CDFER/JLCPCB-Kicad-Library/JLCPCB-Kicad-Footprints/3dModels/CAP-TH_BD8.0-P3.50-D0.6-FD_1.step

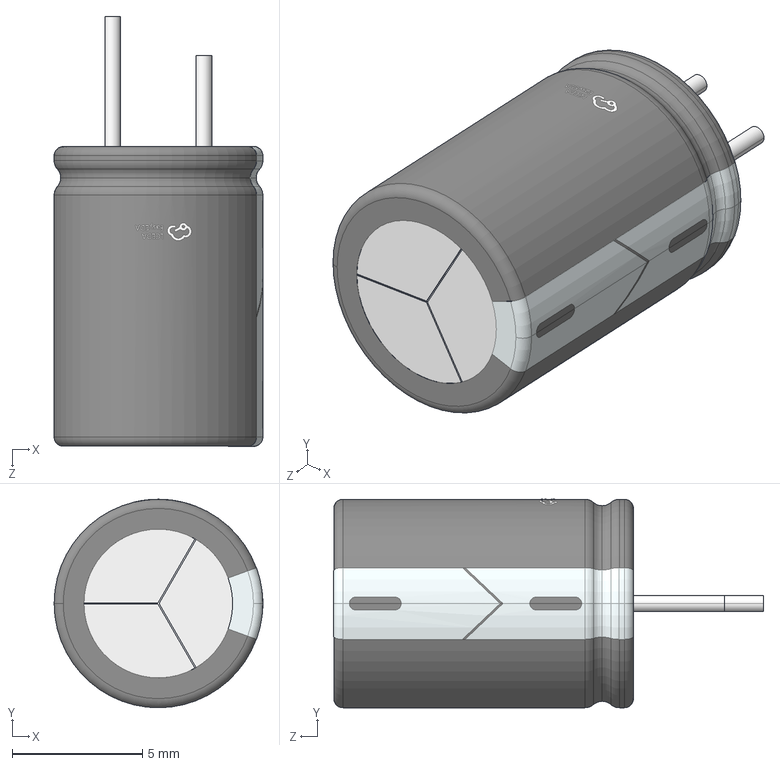
[picture p15: CAD file, 2024-11-15]
JLCPCB-Kicad-Footprints/3dModels/CAP-TH_BD8.0-P3.50-D0.6-FD_1.step
8.01 x 8.00 x 16.5 mm
