CDFER/JLCPCB-Kicad-Library/JLCPCB-Kicad-Footprints/3dModels/RES-SMD_L10.0-W5.2.step

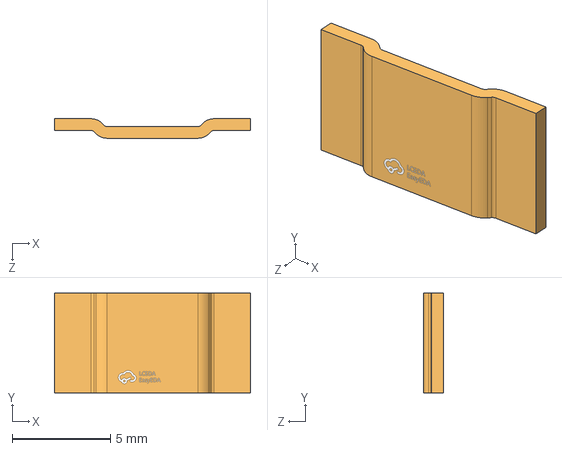
[picture p16: CAD file, 2024-11-15]
JLCPCB-Kicad-Footprints/3dModels/RES-SMD_L10.0-W5.2.step
10.0 x 5.10 x 1.00 mm
