CDFER/JLCPCB-Kicad-Library/JLCPCB-Kicad-Footprints/3dModels/SDB_L8.3-W6.4-P5.10-LS9.9-BL.step

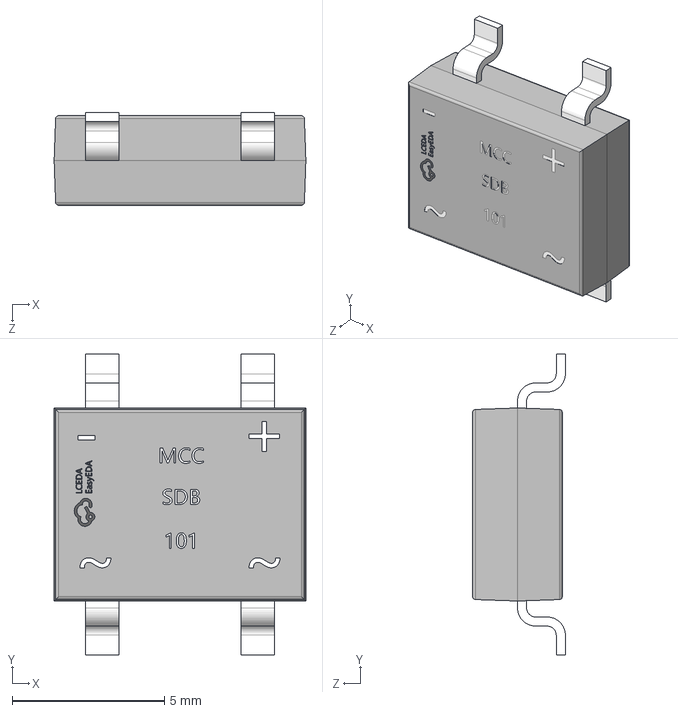
[picture p17: CAD file, 2024-11-15]
JLCPCB-Kicad-Footprints/3dModels/SDB_L8.3-W6.4-P5.10-LS9.9-BL.step
8.28 x 9.90 x 3.05 mm
