CDFER/JLCPCB-Kicad-Library/JLCPCB-Kicad-Footprints/3dModels/IND-SMD_L13.8-W12.6_YSPI13XX.step

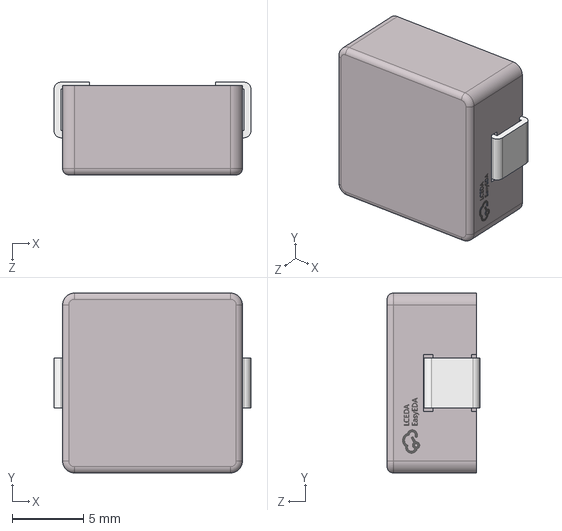
[picture p18: CAD file, 2024-11-15]
JLCPCB-Kicad-Footprints/3dModels/IND-SMD_L13.8-W12.6_YSPI13XX.step
13.8 x 12.6 x 6.50 mm
