CDFER/JLCPCB-Kicad-Library/JLCPCB-Kicad-Footprints/3dModels/CAP-TH_L5.0-W3.2-P5.08-D0.6.step

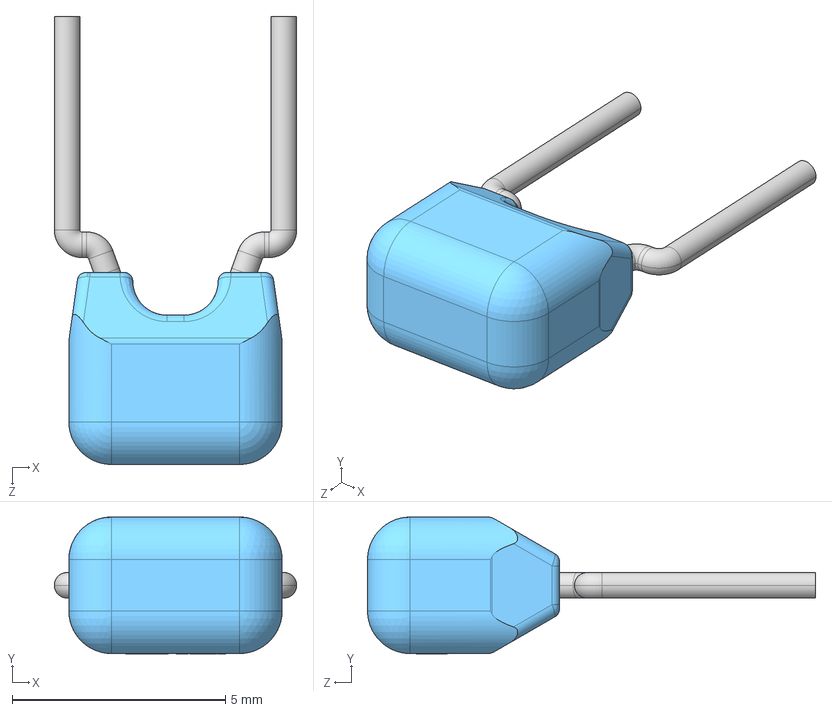
[picture p19: CAD file, 2024-11-15]
JLCPCB-Kicad-Footprints/3dModels/CAP-TH_L5.0-W3.2-P5.08-D0.6.step
5.68 x 3.21 x 10.5 mm
