CDFER/JLCPCB-Kicad-Library/JLCPCB-Kicad-Footprints/3dModels/CAP-TH_BD10.0-P5.00-D0.6-FD.step

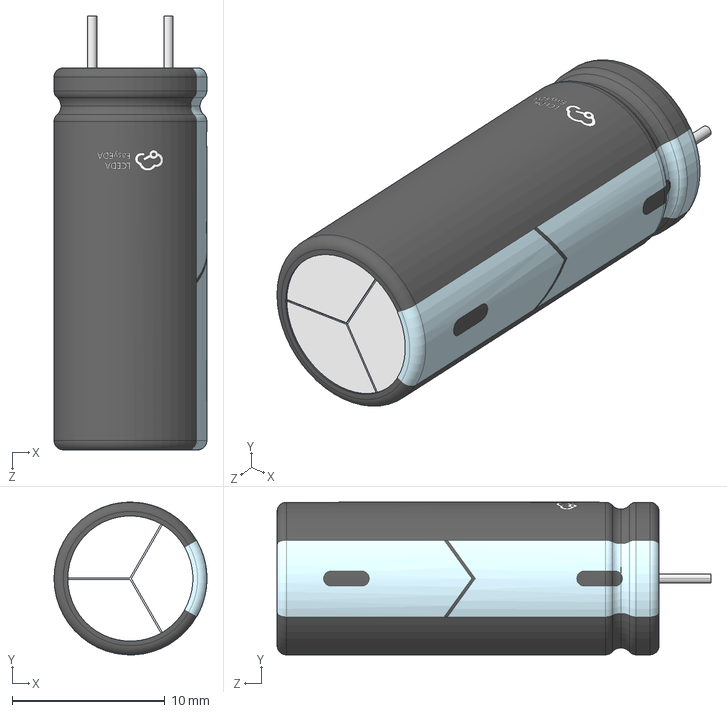
[picture p20: CAD file, 2024-11-15]
JLCPCB-Kicad-Footprints/3dModels/CAP-TH_BD10.0-P5.00-D0.6-FD.step
10.0 x 9.99 x 28.4 mm
