CDFER/JLCPCB-Kicad-Library/JLCPCB-Kicad-Footprints/3dModels/SOT-669_L4.9-W4.0-P1.27-LS6.0-BR.step

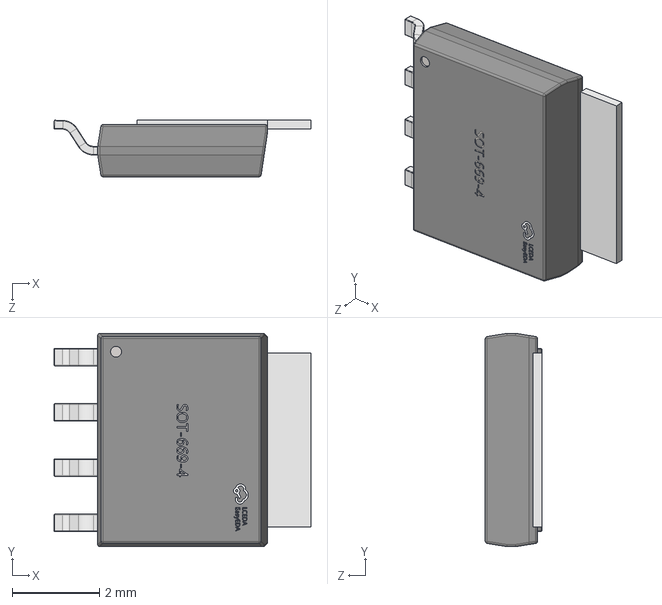
[picture p21: CAD file, 2024-11-15]
JLCPCB-Kicad-Footprints/3dModels/SOT-669_L4.9-W4.0-P1.27-LS6.0-BR.step
5.90 x 4.90 x 1.30 mm
