CDFER/JLCPCB-Kicad-Library/JLCPCB-Kicad-Footprints/3dModels/X3-DFN0603-2_L0.6-W0.3-BI.step

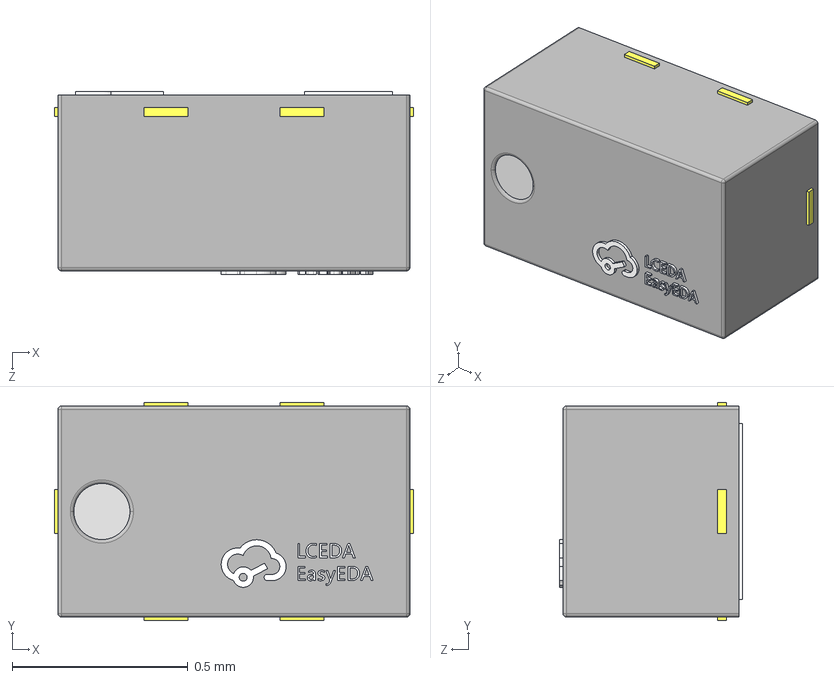
[picture p22: CAD file, 2024-11-15]
JLCPCB-Kicad-Footprints/3dModels/X3-DFN0603-2_L0.6-W0.3-BI.step
1.02 x 0.62 x 0.52 mm
