CDFER/JLCPCB-Kicad-Library/JLCPCB-Kicad-Footprints/3dModels/ITO-220AB-3_L10.0-W4.5-P2.54-L.step

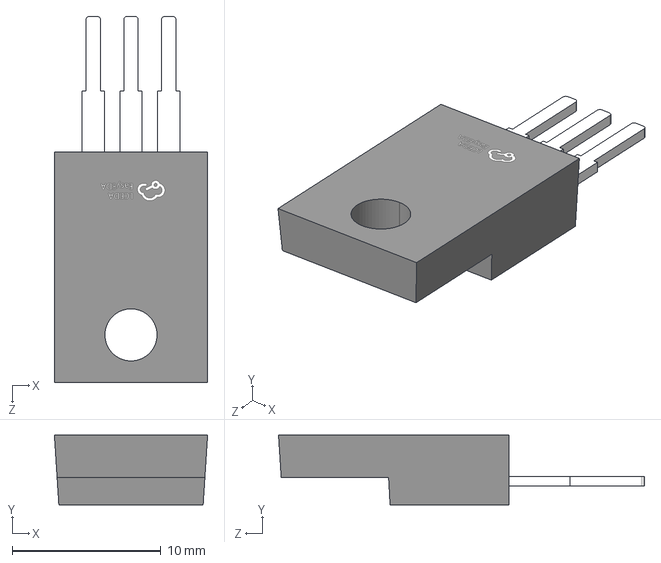
[picture p23: CAD file, 2024-11-15]
JLCPCB-Kicad-Footprints/3dModels/ITO-220AB-3_L10.0-W4.5-P2.54-L.step
10.3 x 4.70 x 24.6 mm
