CDFER/JLCPCB-Kicad-Library/JLCPCB-Kicad-Footprints/3dModels/DO-41_BD1.9-L3.3-P7.30-D0.8-RD.step

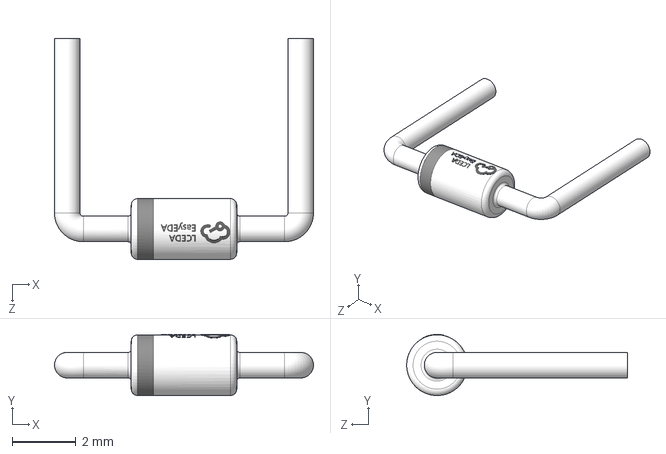
[picture p24: CAD file, 2024-11-15]
JLCPCB-Kicad-Footprints/3dModels/DO-41_BD1.9-L3.3-P7.30-D0.8-RD.step
8.10 x 1.91 x 6.90 mm
