CDFER/JLCPCB-Kicad-Library/JLCPCB-Kicad-Footprints/3dModels/SOP-8_L5.0-W3.8-P1.27-LS6.0-BL.step

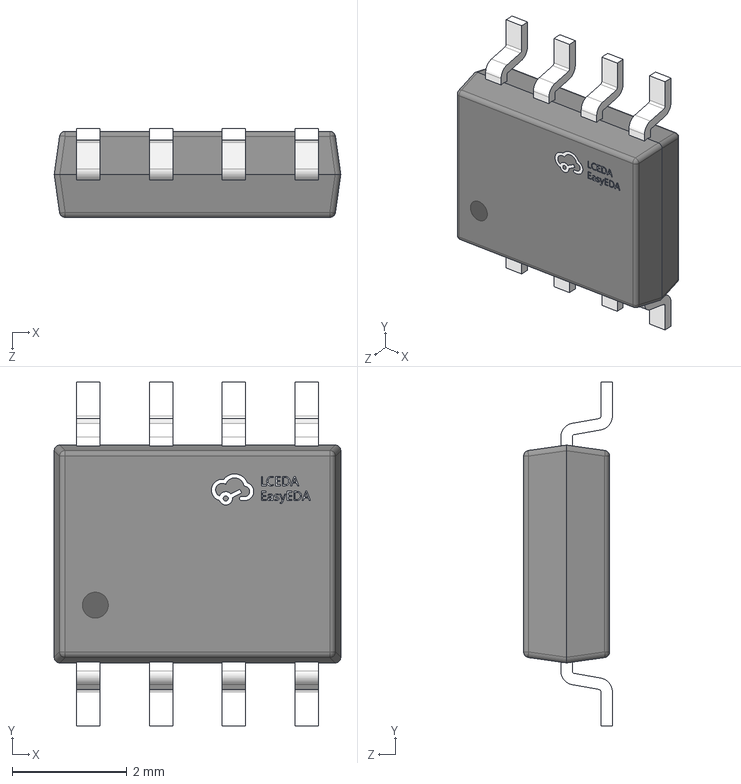
[picture p25: CAD file, 2024-11-15]
JLCPCB-Kicad-Footprints/3dModels/SOP-8_L5.0-W3.8-P1.27-LS6.0-BL.step
5.00 x 6.00 x 1.55 mm
