CDFER/JLCPCB-Kicad-Library/JLCPCB-Kicad-Footprints/3dModels/CAP-TH_BD6.3-P2.50-D1.0-FD.step

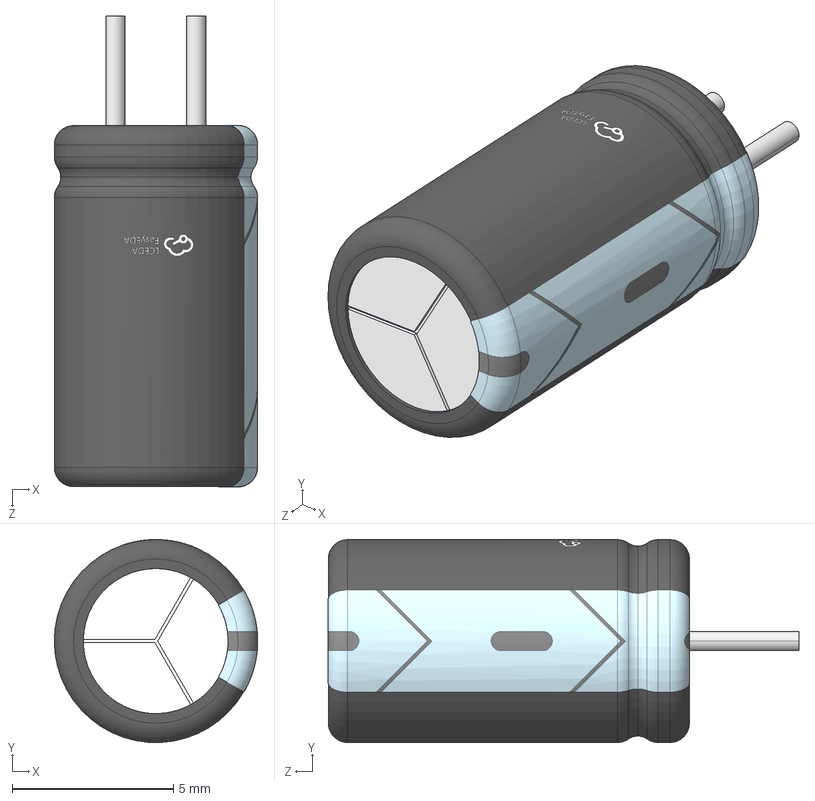
[picture p26: CAD file, 2024-11-15]
JLCPCB-Kicad-Footprints/3dModels/CAP-TH_BD6.3-P2.50-D1.0-FD.step
6.31 x 6.30 x 14.6 mm
