CDFER/JLCPCB-Kicad-Library/JLCPCB-Kicad-Footprints/3dModels/DFS_4P-L8.3-W6.4-P5.10-LS10.1-BL.step

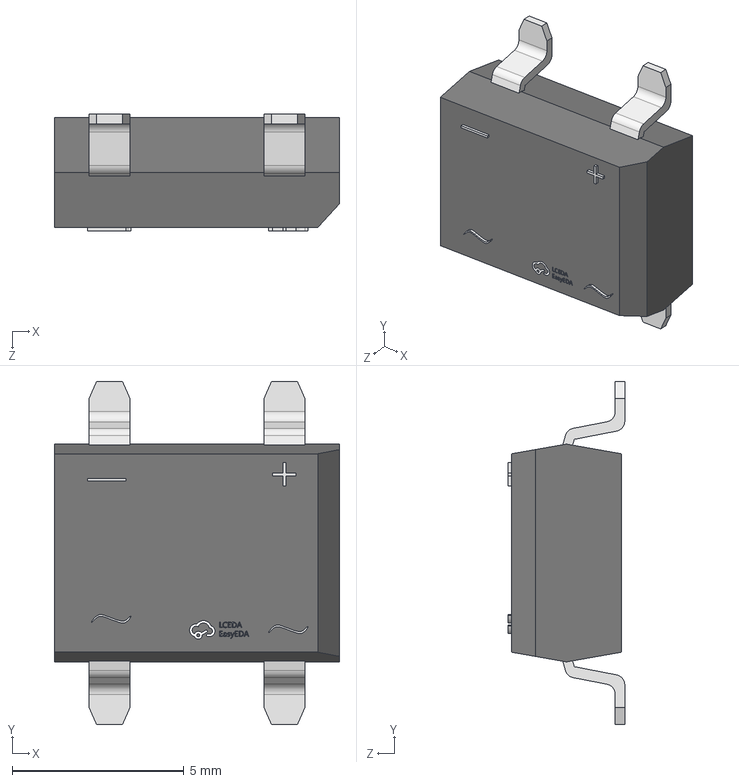
[picture p27: CAD file, 2024-11-15]
JLCPCB-Kicad-Footprints/3dModels/DFS_4P-L8.3-W6.4-P5.10-LS10.1-BL.step
8.32 x 10.0 x 3.40 mm
