CDFER/JLCPCB-Kicad-Library/JLCPCB-Kicad-Footprints/3dModels/C_Plugin,D5xL11mm.step

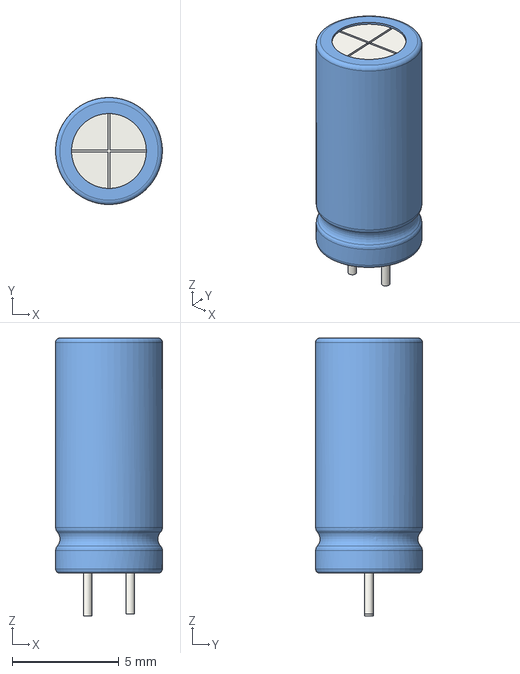
[picture p28: CAD file, 2024-11-15]
JLCPCB-Kicad-Footprints/3dModels/C_Plugin,D5xL11mm.step
5.00 x 5.00 x 13.0 mm
