CDFER/JLCPCB-Kicad-Library/JLCPCB-Kicad-Footprints/3dModels/TO-92-3_L4.9-W3.7-P1.27-L.step

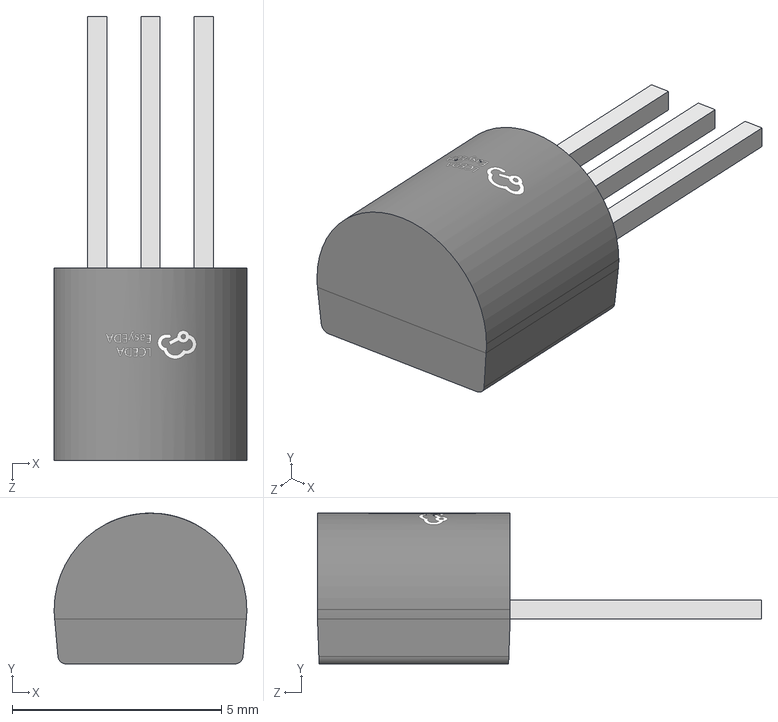
[picture p29: CAD file, 2024-11-15]
JLCPCB-Kicad-Footprints/3dModels/TO-92-3_L4.9-W3.7-P1.27-L.step
4.60 x 3.60 x 10.6 mm
