CDFER/JLCPCB-Kicad-Library/JLCPCB-Kicad-Footprints/3dModels/GBU_4P-L22.0-W3.5-P5.08.step

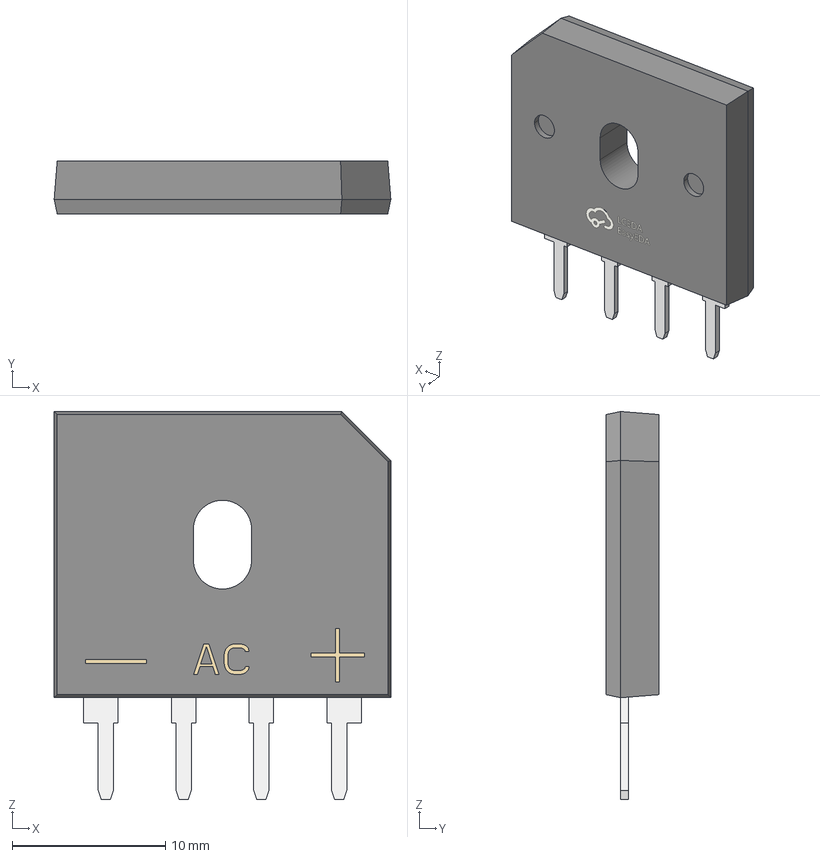
[picture p30: CAD file, 2024-11-15]
JLCPCB-Kicad-Footprints/3dModels/GBU_4P-L22.0-W3.5-P5.08.step
22.0 x 3.48 x 25.4 mm
