CDFER/JLCPCB-Kicad-Library/JLCPCB-Kicad-Footprints/3dModels/GBU810.step

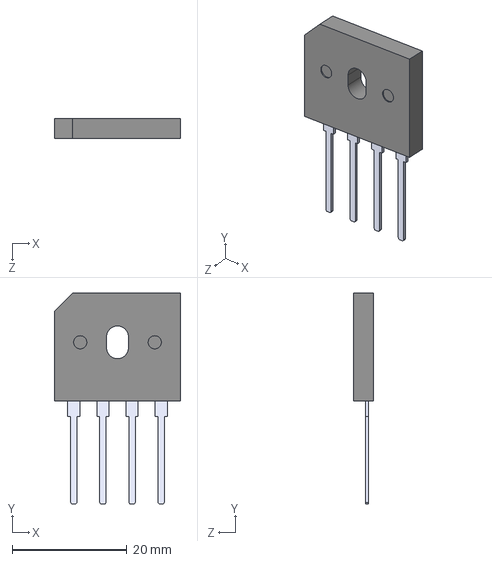
[picture p31: CAD file, 2024-11-15]
JLCPCB-Kicad-Footprints/3dModels/GBU810.step
22.1 x 36.8 x 3.43 mm
