CDFER/JLCPCB-Kicad-Library/JLCPCB-Kicad-Footprints/3dModels/USB-TYPE-C-TH_TYPEC-214-ARP14H105.step

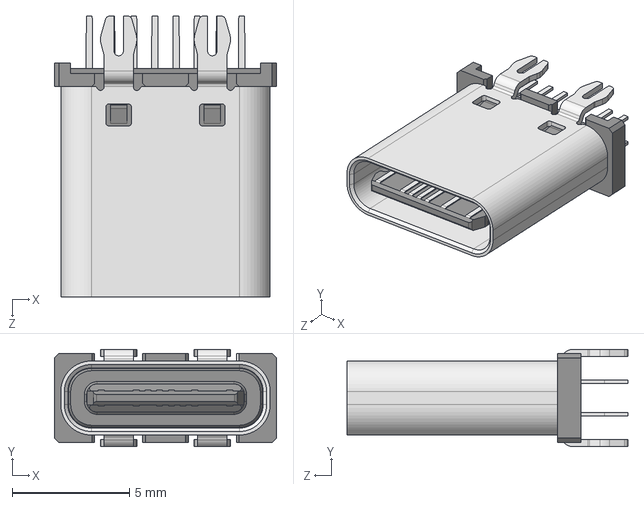
[picture p32: CAD file, 2024-11-15]
JLCPCB-Kicad-Footprints/3dModels/USB-TYPE-C-TH_TYPEC-214-ARP14H105.step
9.50 x 4.16 x 12.0 mm
