CDFER/JLCPCB-Kicad-Library/JLCPCB-Kicad-Footprints/3dModels/LED-SMD_L3.5-W2.8_TVSG-AXBZ-2J8L-1-20-R18-Z.step

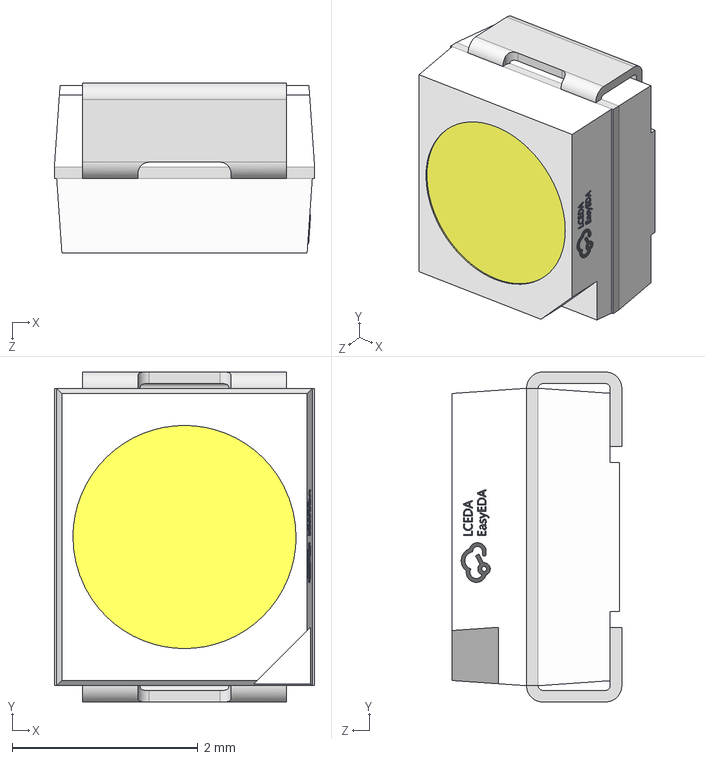
[picture p33: CAD file, 2024-11-15]
JLCPCB-Kicad-Footprints/3dModels/LED-SMD_L3.5-W2.8_TVSG-AXBZ-2J8L-1-20-R18-Z.step
2.80 x 3.55 x 1.83 mm
