CDFER/JLCPCB-Kicad-Library/JLCPCB-Kicad-Footprints/3dModels/SOP-8_L4.9-W3.9-P1.27-LS6.0-BL.step

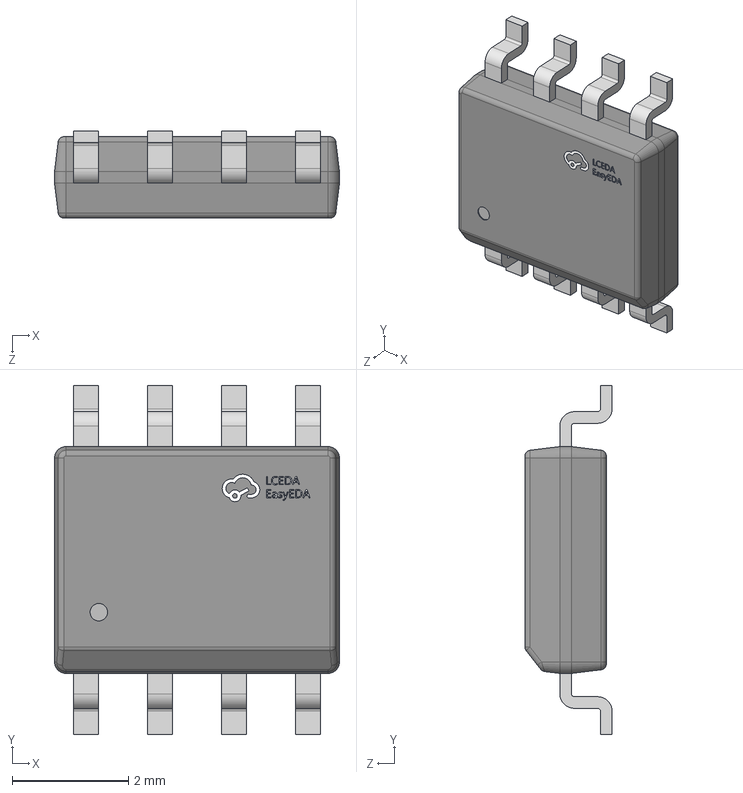
[picture p34: CAD file, 2024-11-15]
JLCPCB-Kicad-Footprints/3dModels/SOP-8_L4.9-W3.9-P1.27-LS6.0-BL.step
4.90 x 6.00 x 1.50 mm
