CDFER/JLCPCB-Kicad-Library/JLCPCB-Kicad-Footprints/3dModels/CAP-TH_BD13.0-P5.00-D0.6-FD.step

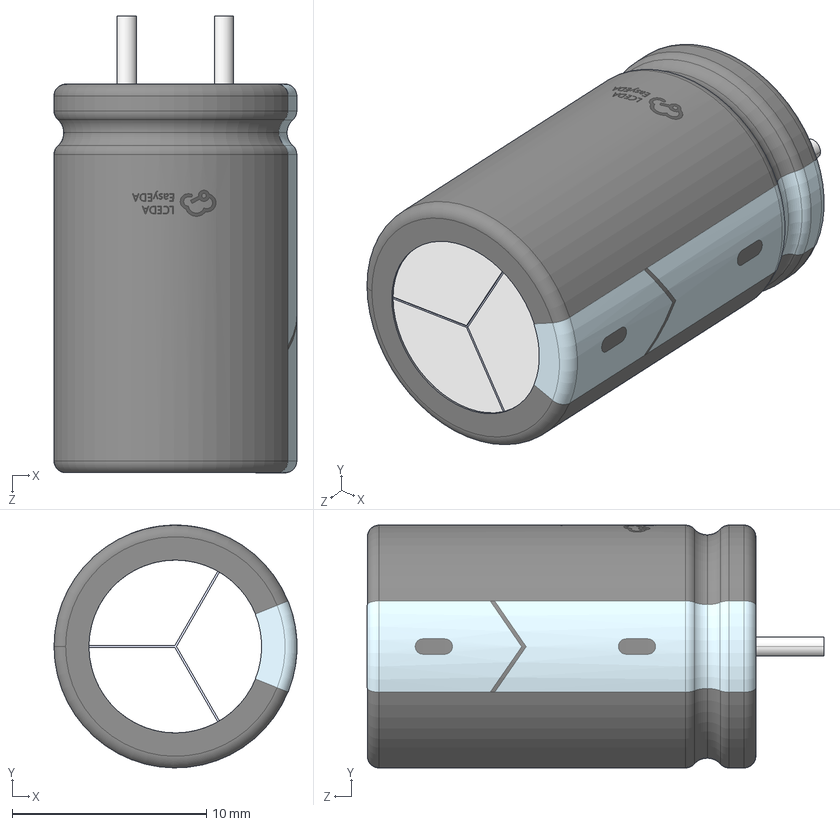
[picture p35: CAD file, 2024-11-15]
JLCPCB-Kicad-Footprints/3dModels/CAP-TH_BD13.0-P5.00-D0.6-FD.step
12.5 x 12.5 x 23.5 mm
