CDFER/JLCPCB-Kicad-Library/JLCPCB-Kicad-Footprints/3dModels/IND-SMD_L7.8-W7.0_GCD75.step

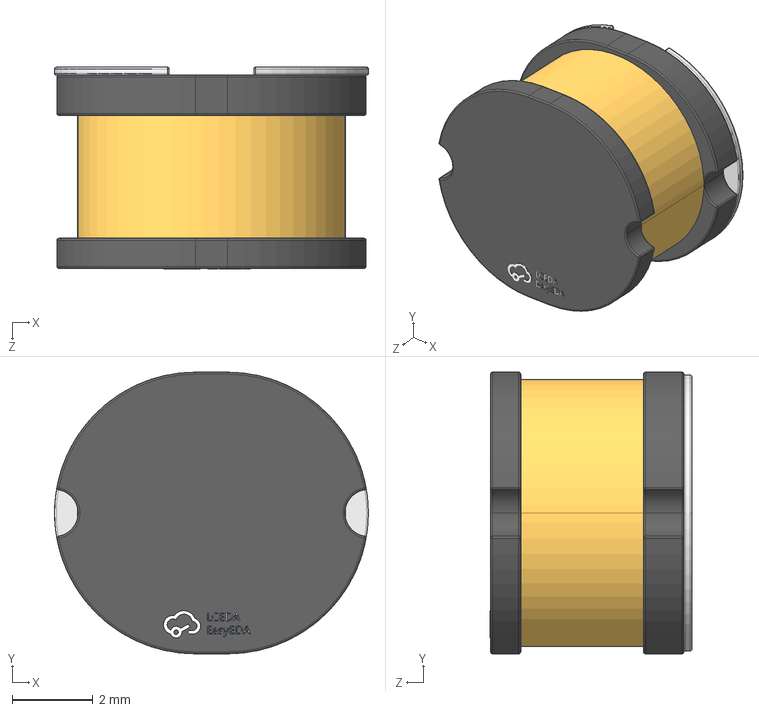
[picture p36: CAD file, 2024-11-15]
JLCPCB-Kicad-Footprints/3dModels/IND-SMD_L7.8-W7.0_GCD75.step
7.80 x 7.00 x 5.01 mm
