CDFER/JLCPCB-Kicad-Library/JLCPCB-Kicad-Footprints/3dModels/MBF-SMD_L4.7-W3.8-P2.50-LS7.0-BL.step

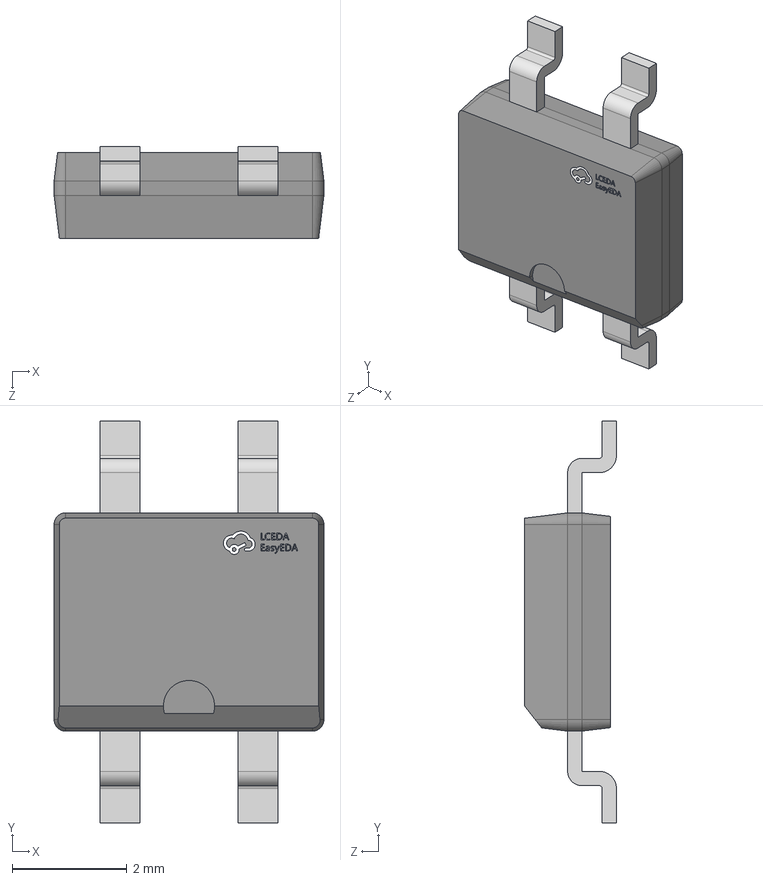
[picture p37: CAD file, 2024-11-15]
JLCPCB-Kicad-Footprints/3dModels/MBF-SMD_L4.7-W3.8-P2.50-LS7.0-BL.step
4.70 x 7.00 x 1.60 mm
