CDFER/JLCPCB-Kicad-Library/JLCPCB-Kicad-Footprints/3dModels/TO-220-3_L9.9-W4.5-P2.54-L-1.step

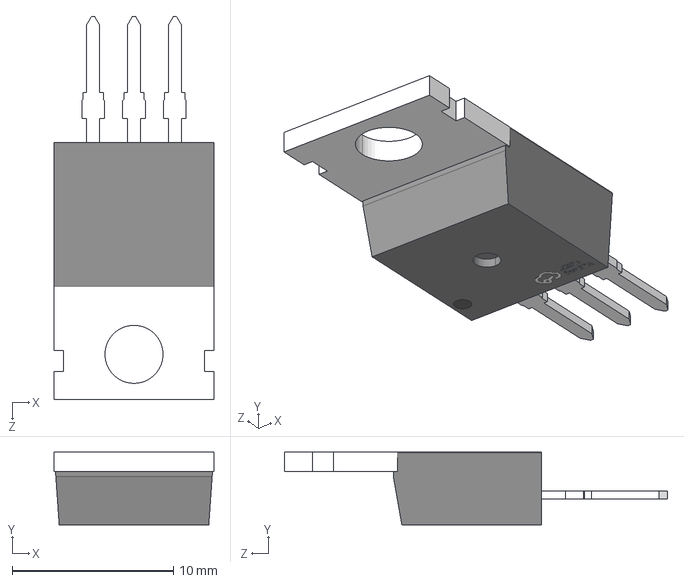
[picture p38: CAD file, 2024-11-15]
JLCPCB-Kicad-Footprints/3dModels/TO-220-3_L9.9-W4.5-P2.54-L-1.step
9.91 x 4.52 x 23.8 mm
