CDFER/JLCPCB-Kicad-Library/JLCPCB-Kicad-Footprints/3dModels/DO-15_BD3.2-L6.4-P10.40-D0.8-RD.step

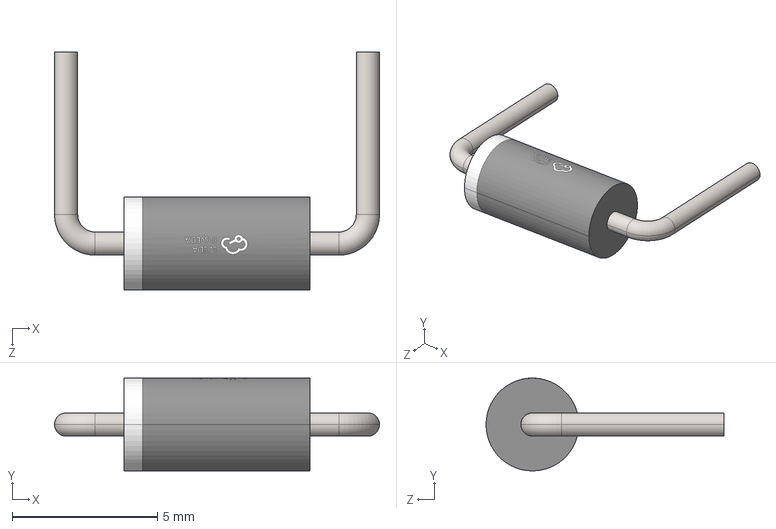
[picture p39: CAD file, 2024-11-15]
JLCPCB-Kicad-Footprints/3dModels/DO-15_BD3.2-L6.4-P10.40-D0.8-RD.step
11.2 x 3.20 x 8.20 mm
