CDFER/JLCPCB-Kicad-Library/JLCPCB-Kicad-Footprints/3dModels/CAP-TH_L5.0-W3.0-P5.00-D0.6-S2.45.step

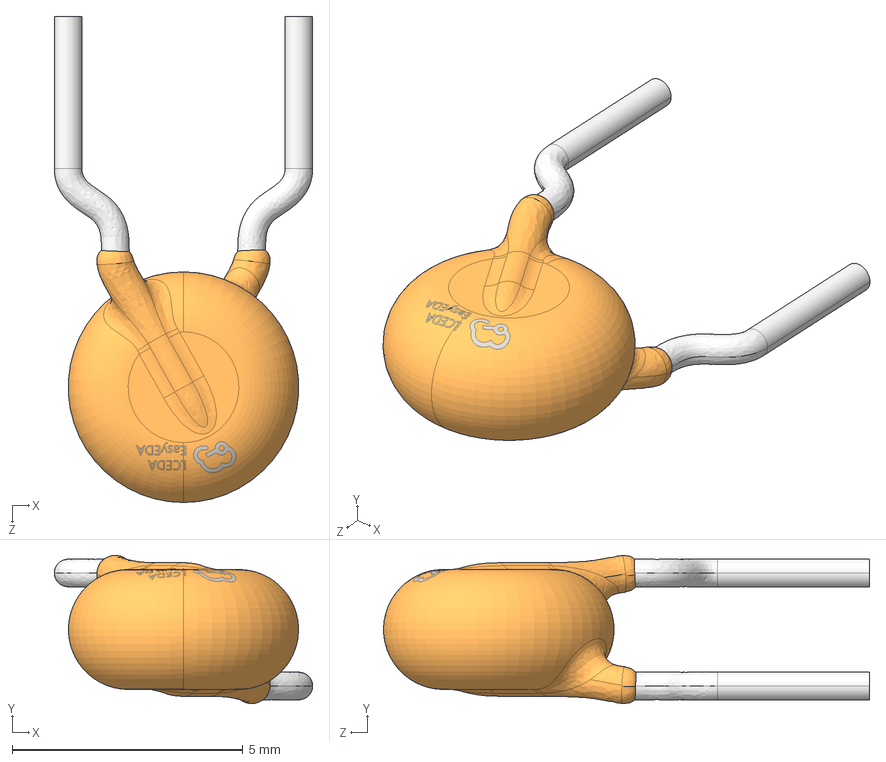
[picture p40: CAD file, 2024-11-15]
JLCPCB-Kicad-Footprints/3dModels/CAP-TH_L5.0-W3.0-P5.00-D0.6-S2.45.step
5.60 x 3.21 x 10.5 mm
