CDFER/JLCPCB-Kicad-Library/JLCPCB-Kicad-Footprints/3dModels/DO-247_L15.6-W5.0-P10.90.step

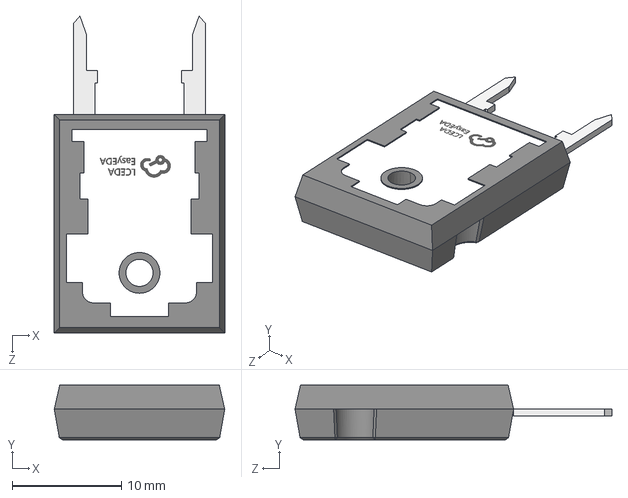
[picture p41: CAD file, 2024-11-15]
JLCPCB-Kicad-Footprints/3dModels/DO-247_L15.6-W5.0-P10.90.step
15.6 x 5.00 x 29.0 mm
