CDFER/JLCPCB-Kicad-Library/JLCPCB-Kicad-Footprints/3dModels/CAP-TH_BD18.0-P7.50-D1.2-FD.step

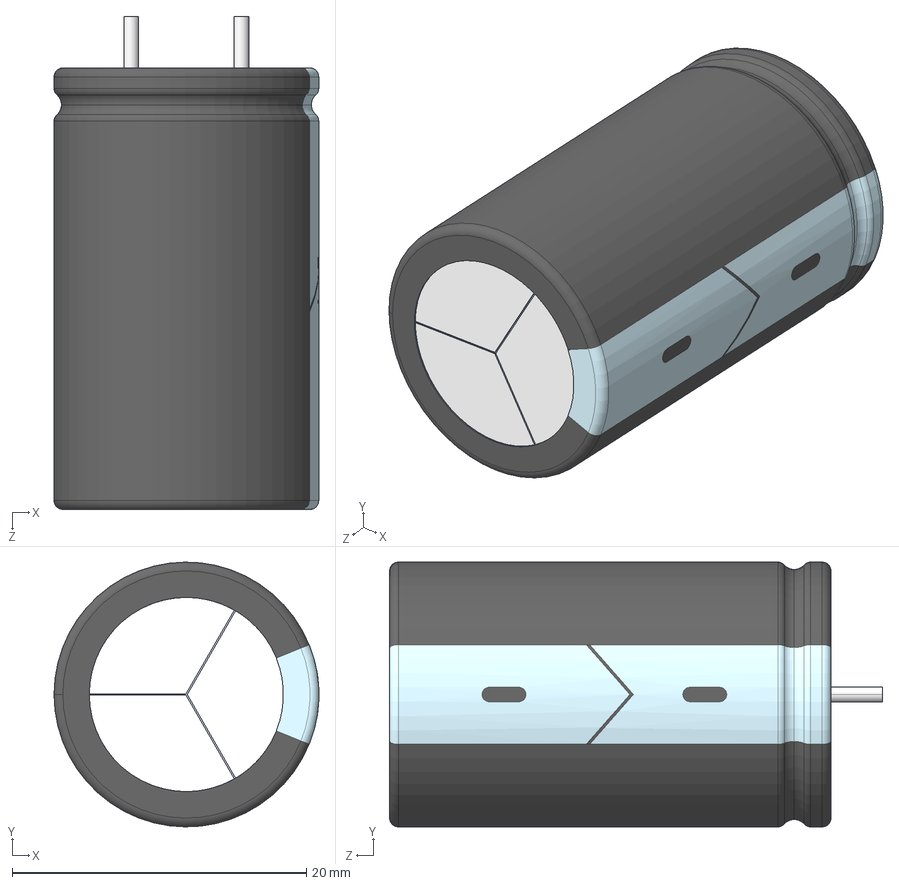
[picture p42: CAD file, 2024-11-15]
JLCPCB-Kicad-Footprints/3dModels/CAP-TH_BD18.0-P7.50-D1.2-FD.step
18.0 x 18.0 x 33.5 mm
