CDFER/JLCPCB-Kicad-Library/JLCPCB-Kicad-Footprints/3dModels/HTSSOP-16_L5.0-W4.4-P0.65-LS6.4-BL-EP-A.step

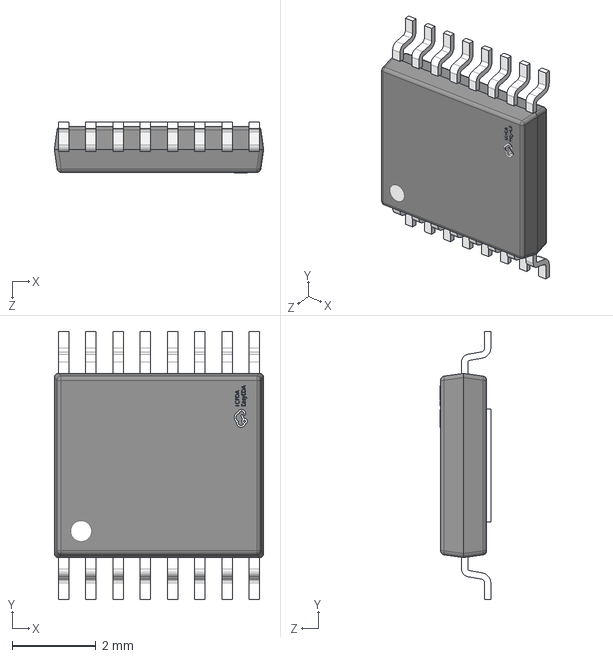
[picture p43: CAD file, 2024-11-15]
JLCPCB-Kicad-Footprints/3dModels/HTSSOP-16_L5.0-W4.4-P0.65-LS6.4-BL-EP-A.step
5.00 x 6.40 x 1.21 mm
