CDFER/JLCPCB-Kicad-Library/JLCPCB-Kicad-Footprints/3dModels/SOD-523F_L1.7-W0.9-LS1.7-RD.step

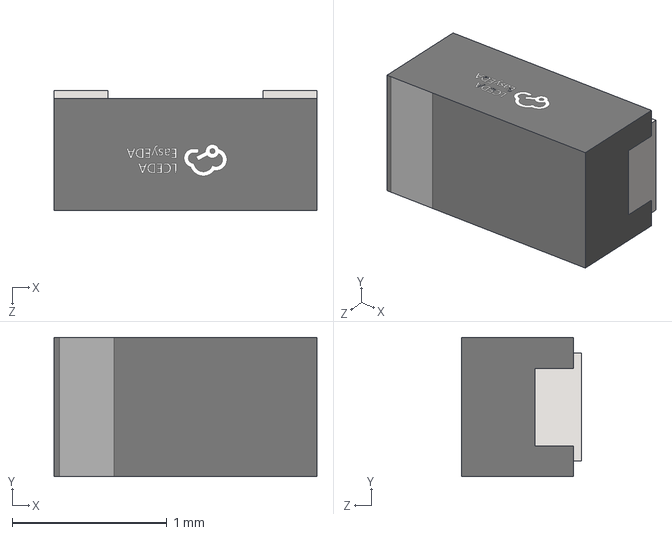
[picture p44: CAD file, 2024-11-15]
JLCPCB-Kicad-Footprints/3dModels/SOD-523F_L1.7-W0.9-LS1.7-RD.step
1.70 x 0.901 x 0.775 mm
