CDFER/JLCPCB-Kicad-Library/JLCPCB-Kicad-Footprints/3dModels/CAP-TH_BD18.0-P7.5-D0.8-FD.step

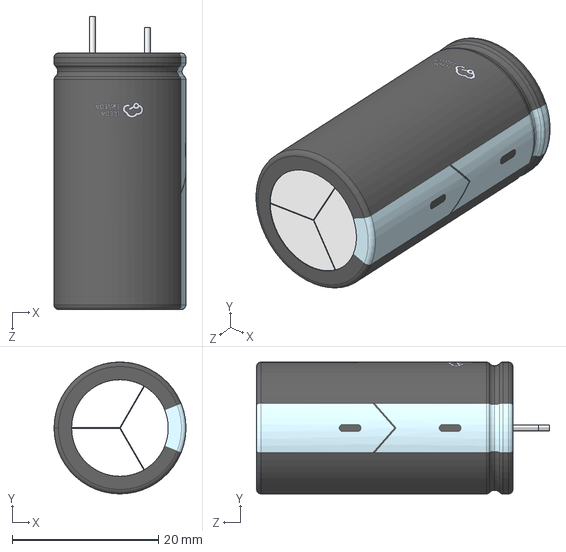
[picture p45: CAD file, 2024-11-15]
JLCPCB-Kicad-Footprints/3dModels/CAP-TH_BD18.0-P7.5-D0.8-FD.step
18.0 x 18.0 x 40.0 mm
