CDFER/JLCPCB-Kicad-Library/JLCPCB-Kicad-Footprints/3dModels/IND-SMD_L10.3-W10.3_1274AS-H-330M.step

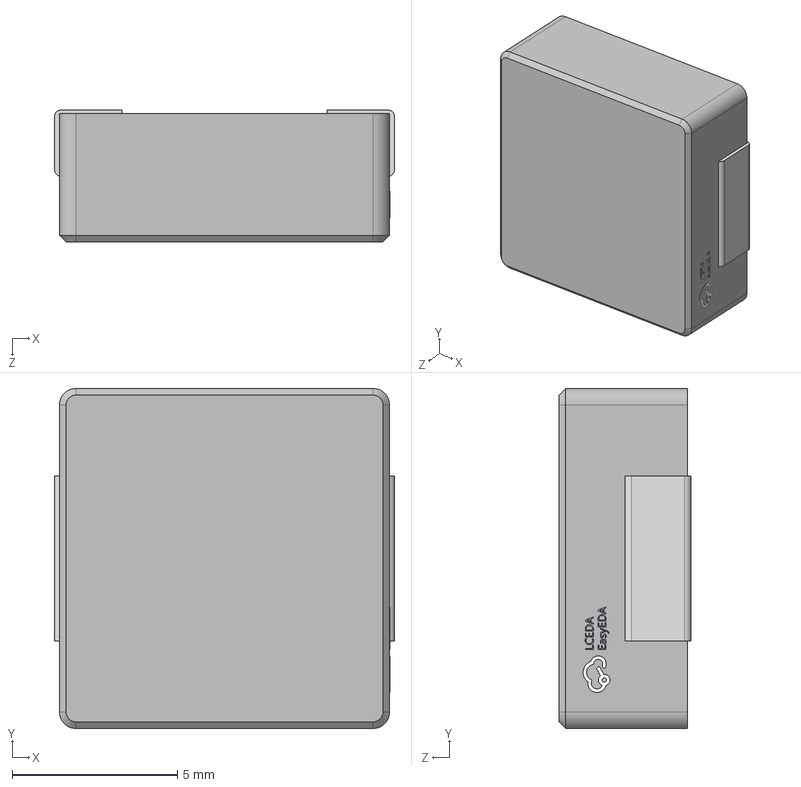
[picture p46: CAD file, 2024-11-15]
JLCPCB-Kicad-Footprints/3dModels/IND-SMD_L10.3-W10.3_1274AS-H-330M.step
10.3 x 10.3 x 4.00 mm
