CDFER/JLCPCB-Kicad-Library/JLCPCB-Kicad-Footprints/3dModels/RES-TH_L12.5-W6.7-P7.50-D1.2.step

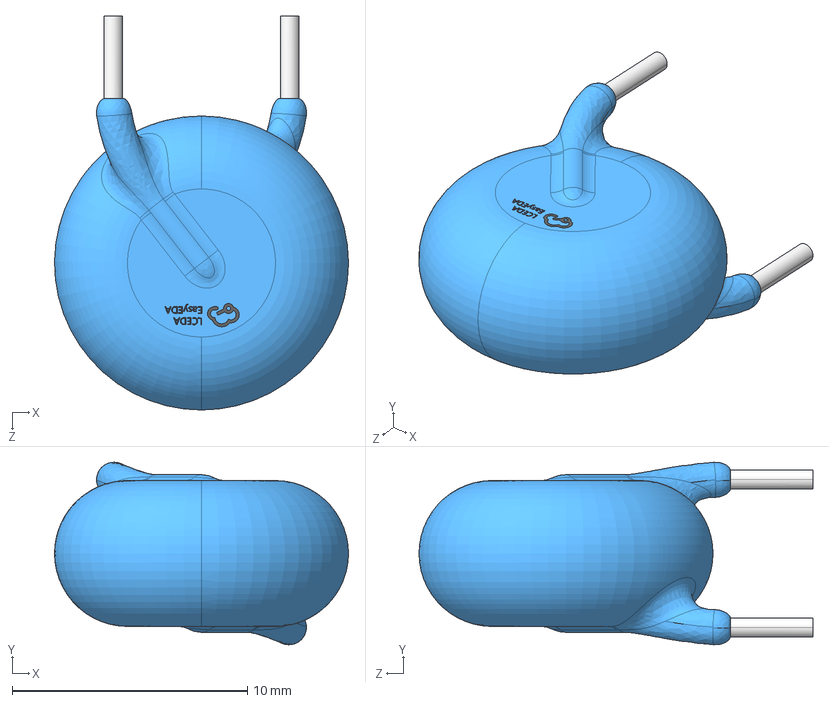
[picture p47: CAD file, 2024-11-15]
JLCPCB-Kicad-Footprints/3dModels/RES-TH_L12.5-W6.7-P7.50-D1.2.step
12.5 x 7.76 x 16.8 mm
